wolfwood/printed-keycap-mods/util/logic.scad

function xor(a,b) = (a && !b) || (!a && b);
