wolfwood/printed-keycap-mods/CS/CS-bindings/convex.scad

use <../../includes/PseudoMakeMeKeyCapProfiles/Choc_Chicago_Steno_Convex.scad>;

module convex_key(key="R3x", homing=false) {
  keyID = key == "R2x" ? 0 :
    key == "R3x" ? 1 :
    assert(false, str("invalid CS thumb key ID: ", key));

  keycap(keyID   = keyID, //change profile refer to KeyParameters Struct
	 cutLen  = 0, //Don't change. for chopped caps
	 Stem    = true, //tusn on shell and stems
	 StemRot = 0, //change stem orientation by deg
	 Dish    = true, //turn on dish cut
	 Stab    = 0,
	 visualizeDish = false, // turn on debug visual of Dish
	 crossSection  = false, // center cut to check internal
	 homeDot = homing, //turn on homedots
	 Legends = false
	 );
}

convex_key();
